vives-projectwerk-2-2020/LoRaWAN-antenna/img/antenne_868MHz.jpg

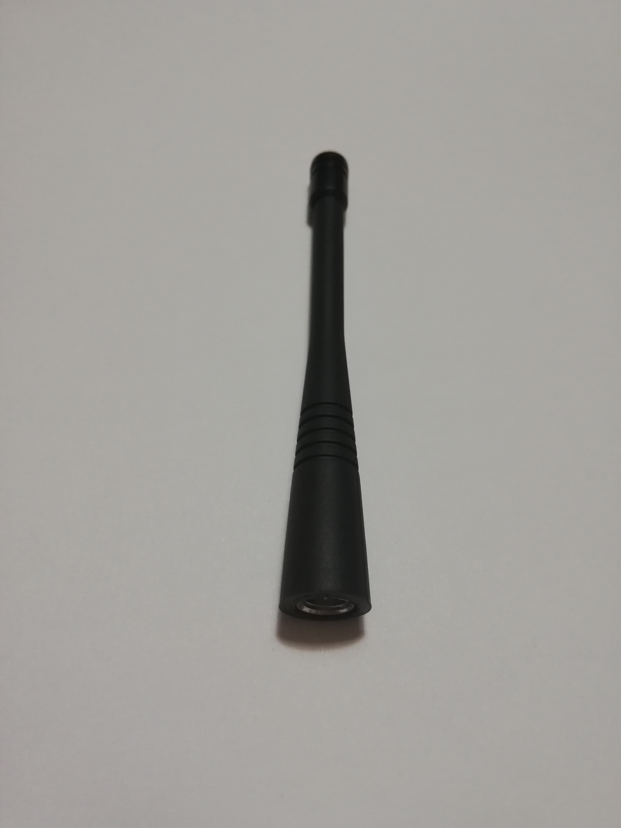
img/antenne_868MHz.jpg
