vives-projectwerk-2-2020/LoRaWAN-antenna/img/antenne_backup_868MHz.jpg

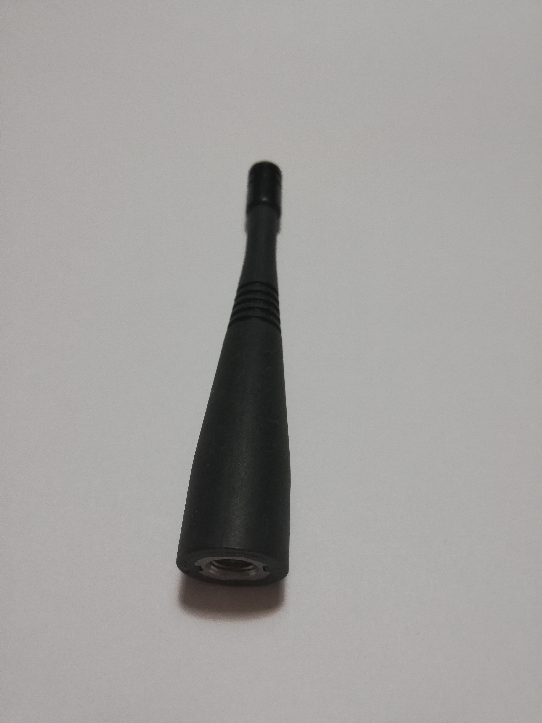
img/antenne_backup_868MHz.jpg
